jsatterla/LabIIIGroup2/Biomedical/EKG/oldekggraph.JPG

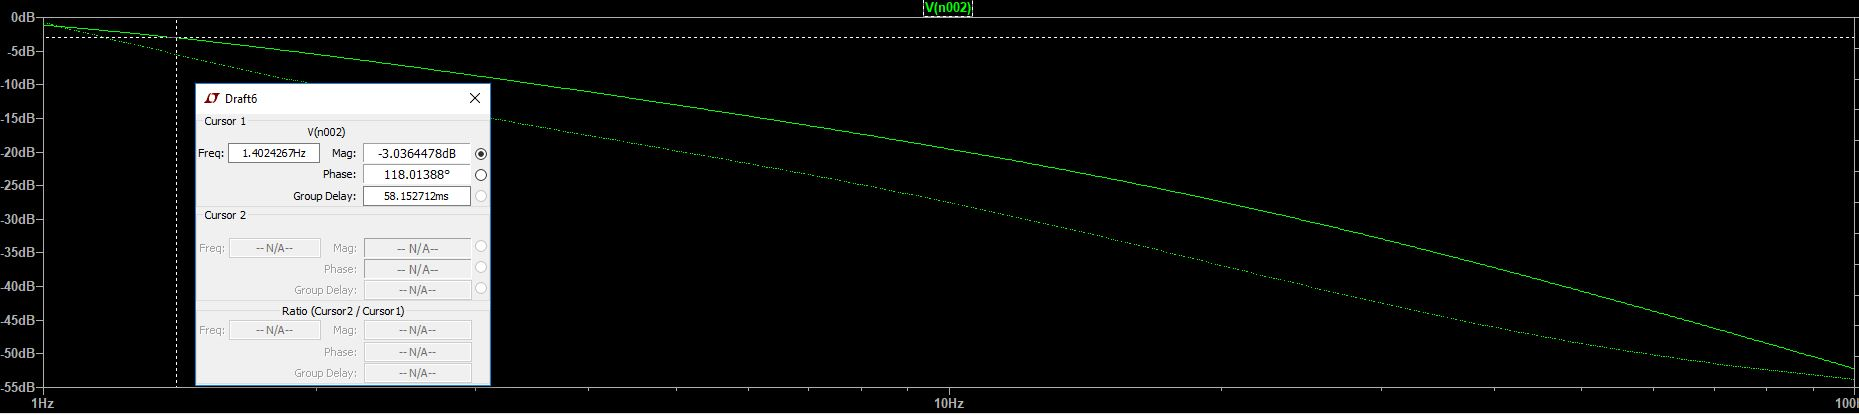
Biomedical/EKG/oldekggraph.JPG
