jsatterla/LabIIIGroup2/Biomedical/EKG/oldekgsch.JPG

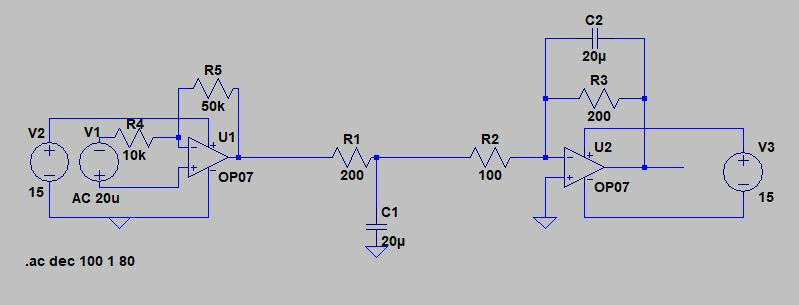
Biomedical/EKG/oldekgsch.JPG
